niccit/easy-remote/secrets_example.py

# Documentation for internet connect with the Matrix Portal
# can be found https://learn.adafruit.com/adafruit-matrixportal-m4/internet-connect
secrets = {
    'ssid': '<your ssid here>',
    'password': '<password for your network>',
    'timezone': '<example: America/New_York',  # See http://worldtimeapi.org/timezones
    'aio_username': '<your Adafruit IO username>',  # See https://io.adafruit.com
    'aio_key': '<your Adafruit IO key>'
}
